rawrrudy/jalrakshak/docs/images/JalRakshak-Upd-Label.png

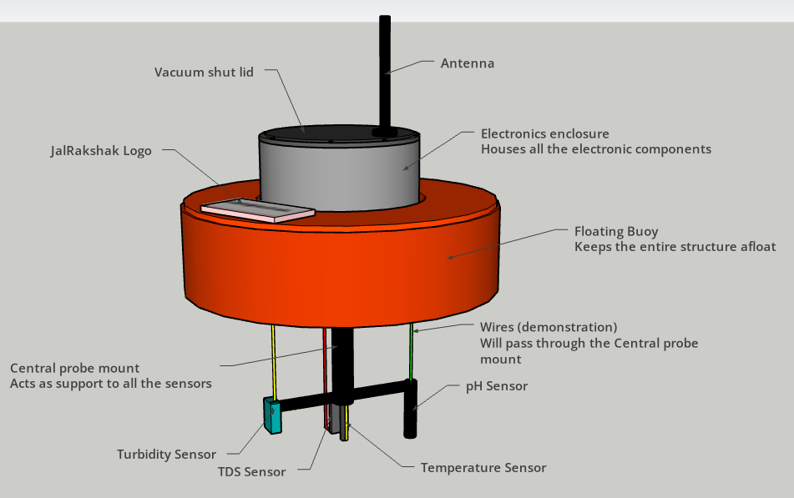
docs/images/JalRakshak-Upd-Label.png
